shengwen-tw/nixie-clock/material/atmega328_interrupt.png

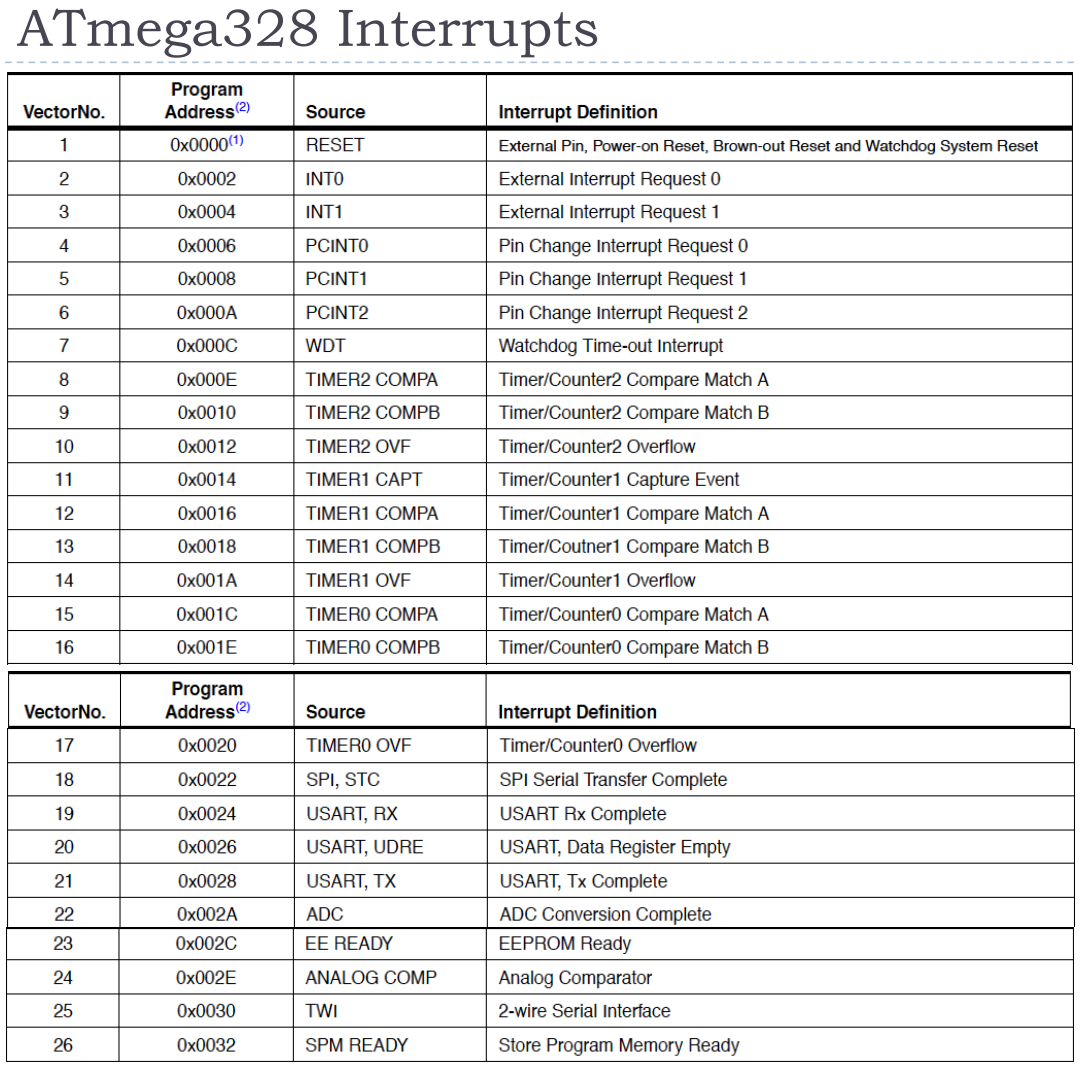
material/atmega328_interrupt.png
