shengwen-tw/nixie-clock/firmware/firmware/nixie_clock/pindef.h

#ifndef __PIN_DEF_H
#define __PIN_DEF_H

//K155IDI
extern int pin_font_a, pin_font_b, pin_font_c, pin_font_d;

extern int pin_font_left_dot, pin_font_right_dot;

//HEF4028
extern int pin_tube_select_a0, pin_tube_select_a1, pin_tube_select_a2, pin_tube_select_a3;

extern int pin_brightness;

//Buttons
extern int pin_play_button, pin_adjust_button, pin_mode_button;

//MP3
extern int mp3_rx, mp3_tx, mp3_state;

#endif
