shengwen-tw/nixie-clock/firmware/obsoleted/nixie_clock/event.h

#ifndef __EVENT_H__
#define __EVENT_H__

/* Button base class */
class buttonBase {
  protected:
      int button_pin;
      clock_time *clock;
      /* Timer related variable */
      int hold_time;
      bool time_record_flag;
      
  public:
      /* Class constructor */
      buttonBase(int button_pin, clock_time *clock);
      /* Timer related functions */
      bool get_timer_flag();
      void timer_enable();
      void timer_disable();
      void hold_time_inc();
      /* Button event handler */
      virtual void button_click() = 0;
};

/* Implementations of the button */
class searchButton : public buttonBase {
  public:
      /* Class constructor */
      searchButton(int button_pin, clock_time *clock) : buttonBase(button_pin, clock) {}
      /* Button event handler */
      void button_click();
};

class adjustButton : public buttonBase {
  private:
      bool mode_changed;
  public:
      /* Class constructor */
      adjustButton(int button_pin, clock_time *clock) : buttonBase(button_pin, clock) { mode_changed = false; }
      /* Button event handler */
      void button_click();
};

class modeButton : public buttonBase {
  public:
      /* Class constructor */
      modeButton(int button_pin, clock_time *clock) : buttonBase(button_pin, clock) {}
      /* Button event handler */
      void button_click();
};

#endif
